msus/PCB-Business-card/PCB-XO_MSP4302553/Application/structure.c

//******************************************************************************
// structure.c
// 
// Touch the element to turn on/off the LED
// RO method capactiance measurement using PinOsc IO, TimerA0, and WDT+
//
//******************************************************************************

#include "structure.h"

// Element (P3.7)
const struct Element middle_element = {

              .inputPxselRegister = (uint8_t *)&P3SEL,
              .inputPxsel2Register = (uint8_t *)&P3SEL2,
              .inputBits = BIT7,
              // When using an abstracted function to measure the element
              // the 100*(maxResponse - threshold) < 0xFFFF
              // ie maxResponse - threshold < 655
              .maxResponse = 500+655,
              .threshold = 500
};

// One Button Sensor
const struct Sensor one_button =
               { 
                  .halDefinition = RO_PINOSC_TA0_WDTp,	// Sensing Method
                  .numElements = 1,						// # of Elements
                  .baseOffset = 0,						// First element index = 0
                  // Pointer to elements
                  .arrayPtr[0] = &middle_element,  		// point to middle element
                  // Timer Information
                  .measGateSource= GATE_WDT_ACLK,     //  0->SMCLK, 1-> ACLK
                  .accumulationCycles= WDTp_GATE_64   //64 - Default                                                
               };
